Siddharth2308/Flight-Controller-Esp32-Coreless/assets/images/2.jpg

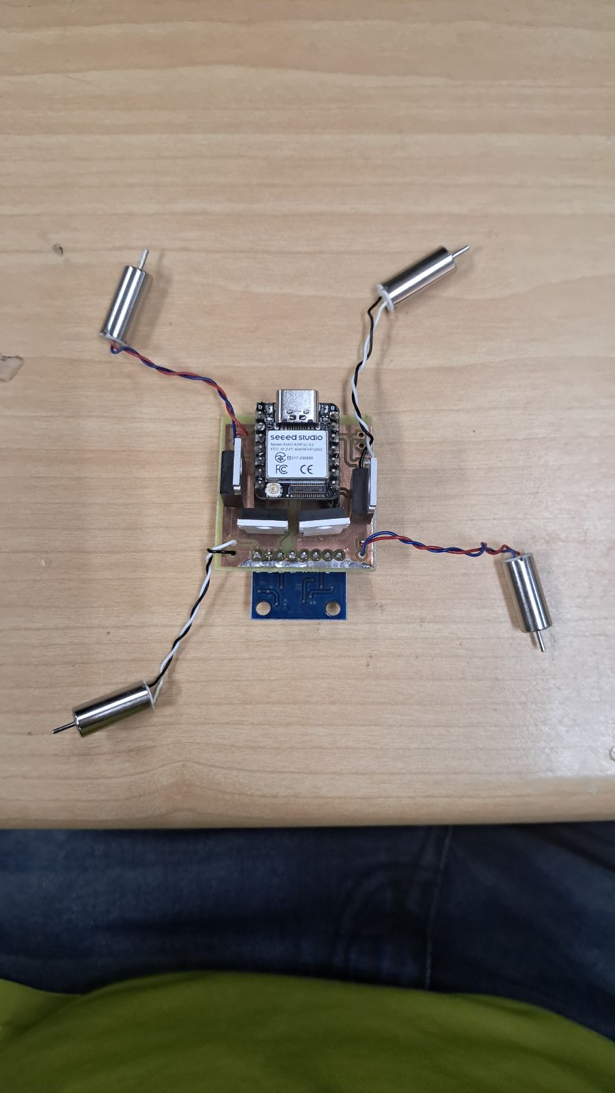
assets/images/2.jpg
