Siddharth2308/Flight-Controller-Esp32-Coreless/assets/images/3.jpg

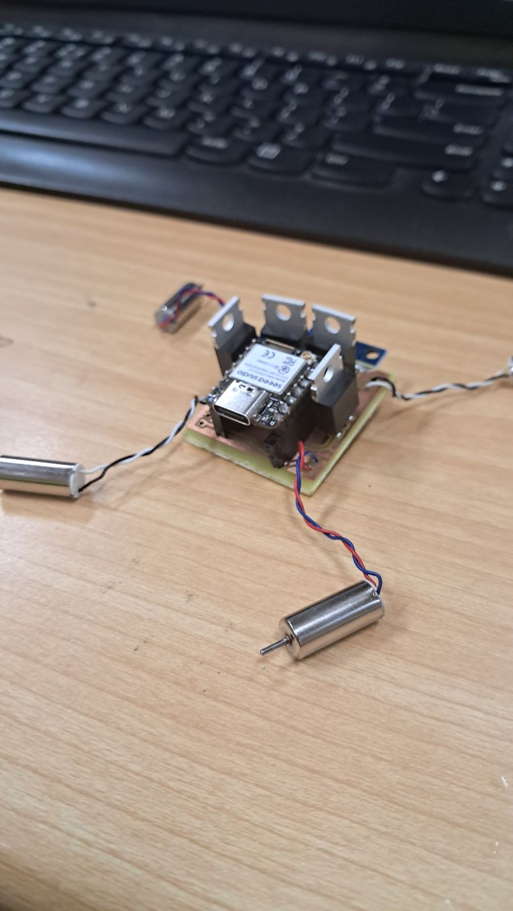
assets/images/3.jpg
