Siddharth2308/Flight-Controller-Esp32-Coreless/assets/images/4.jpg

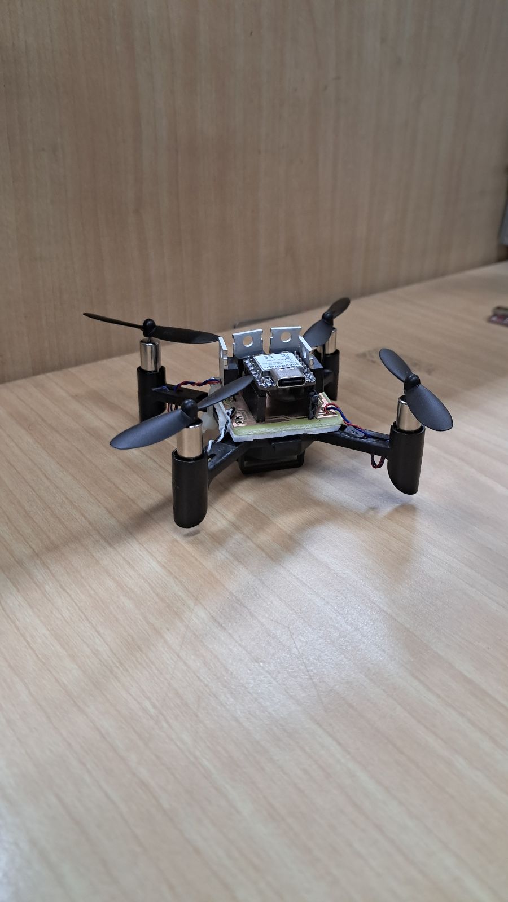
assets/images/4.jpg
