Siddharth2308/Flight-Controller-Esp32-Coreless/assets/images/5.jpg

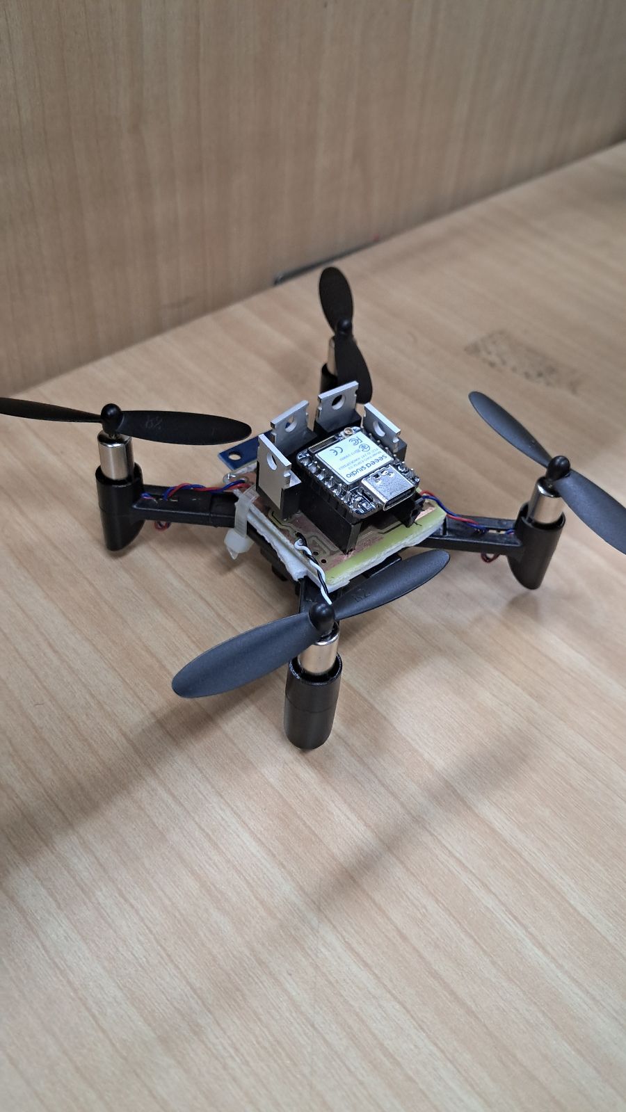
assets/images/5.jpg
