Siddharth2308/Flight-Controller-Esp32-Coreless/assets/images/6.jpg

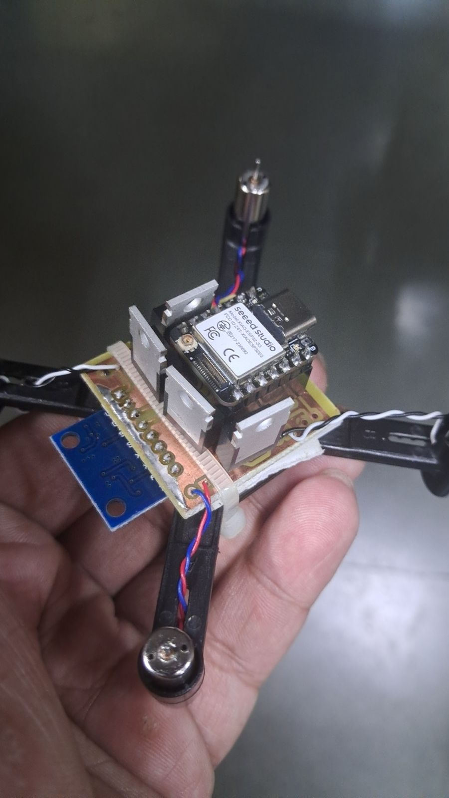
assets/images/6.jpg
